spitzlbergerj/CarreraBoxenManager/images/AnsichtHinten.png

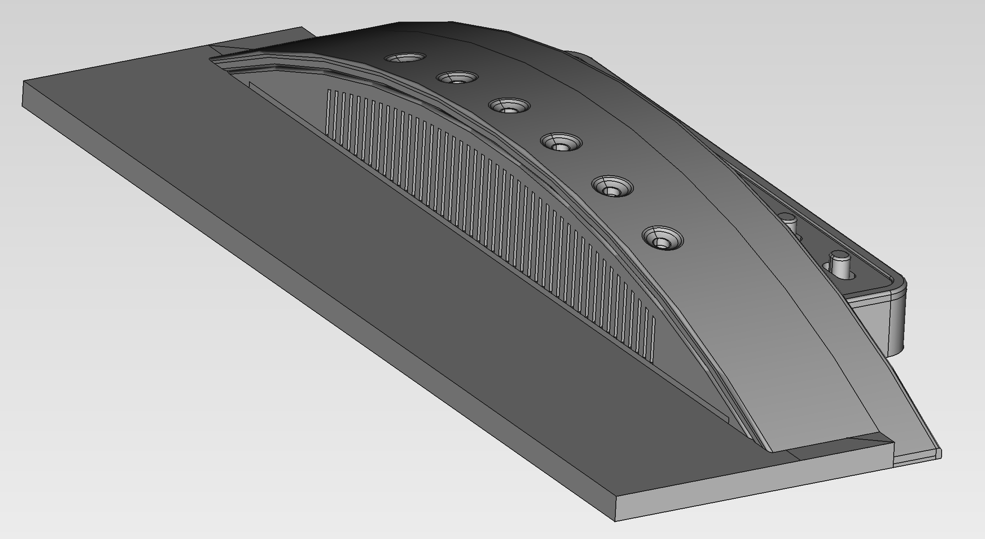
images/AnsichtHinten.png
