spitzlbergerj/CarreraBoxenManager/images/BoxenManager-LED-Platine.jpg

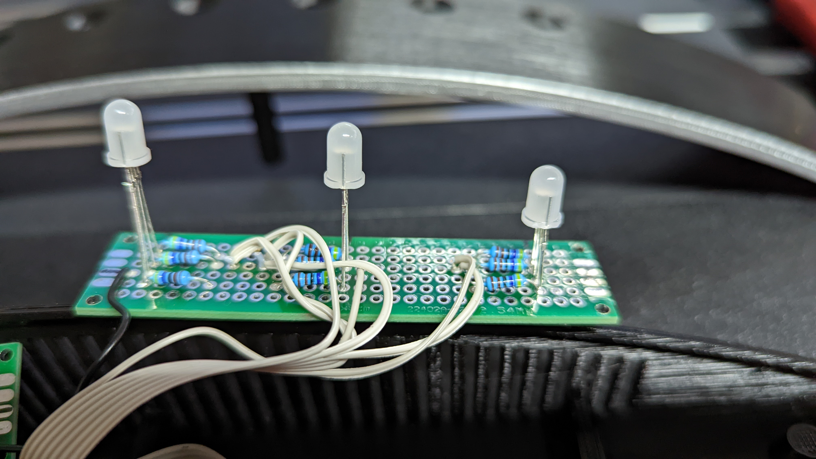
images/BoxenManager-LED-Platine.jpg
