spitzlbergerj/CarreraBoxenManager/images/Boxenmanager-Schiene-Endgehaeuse-Unteransicht.jpg

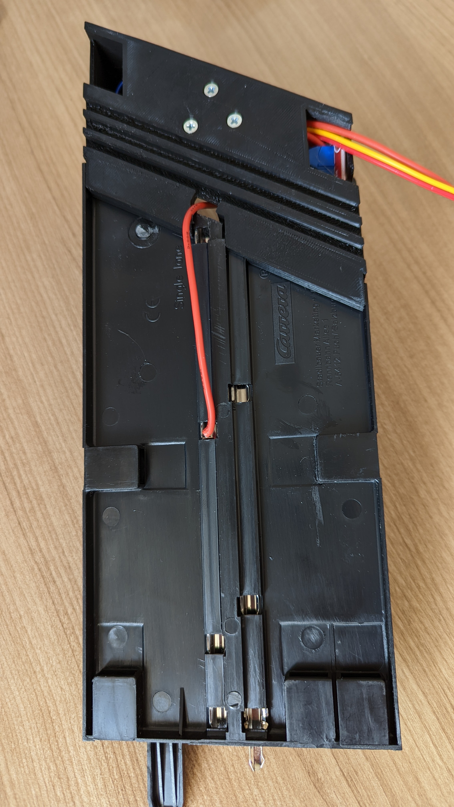
images/Boxenmanager-Schiene-Endgehaeuse-Unteransicht.jpg
