spitzlbergerj/CarreraBoxenManager/images/BoxenManager-Schienenendgehaeuse.jpg

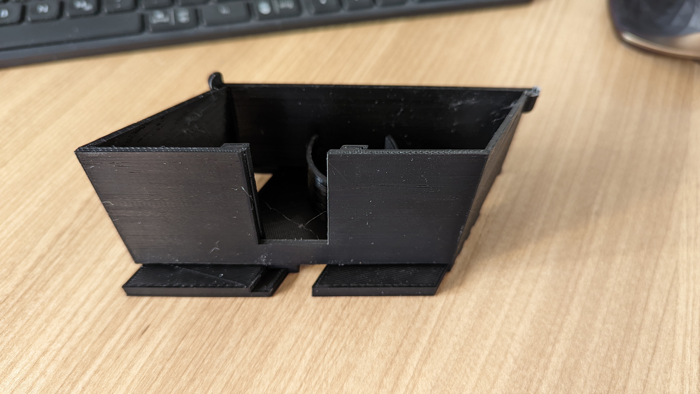
images/BoxenManager-Schienenendgehaeuse.jpg
