spitzlbergerj/CarreraBoxenManager/images/BoxenManager-unter-Bogen-1.jpg

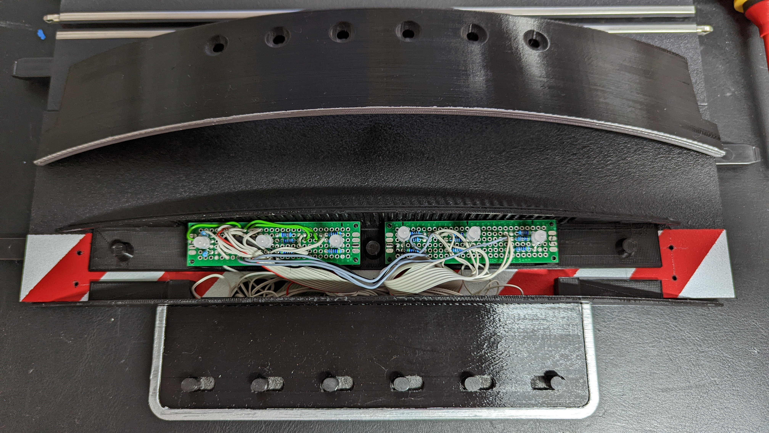
images/BoxenManager-unter-Bogen-1.jpg
