spitzlbergerj/CarreraBoxenManager/images/BoxenManager-Unterseite-1.jpg

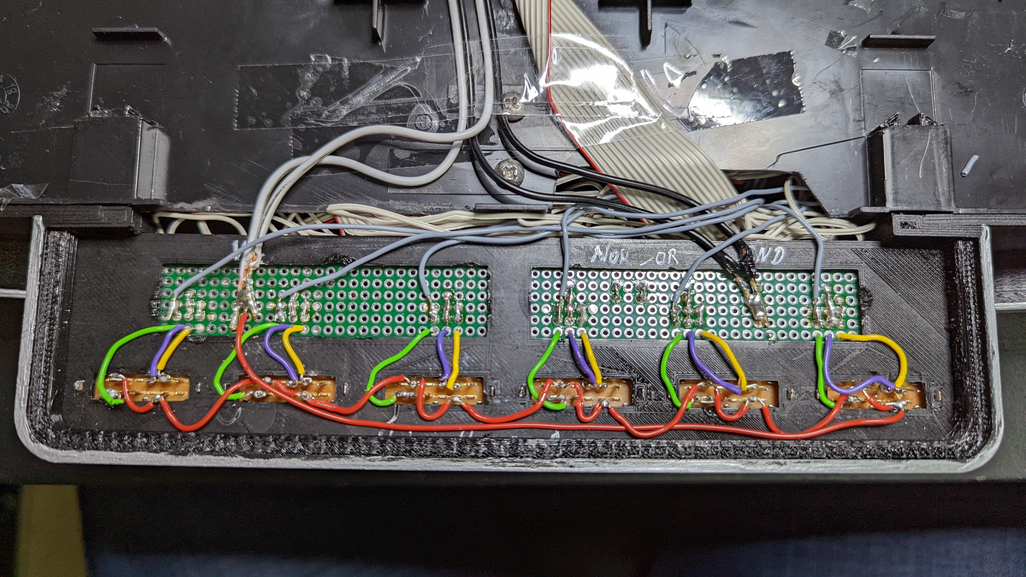
images/BoxenManager-Unterseite-1.jpg
