spitzlbergerj/CarreraBoxenManager/images/BoxenManager-Unterseite-2.jpg

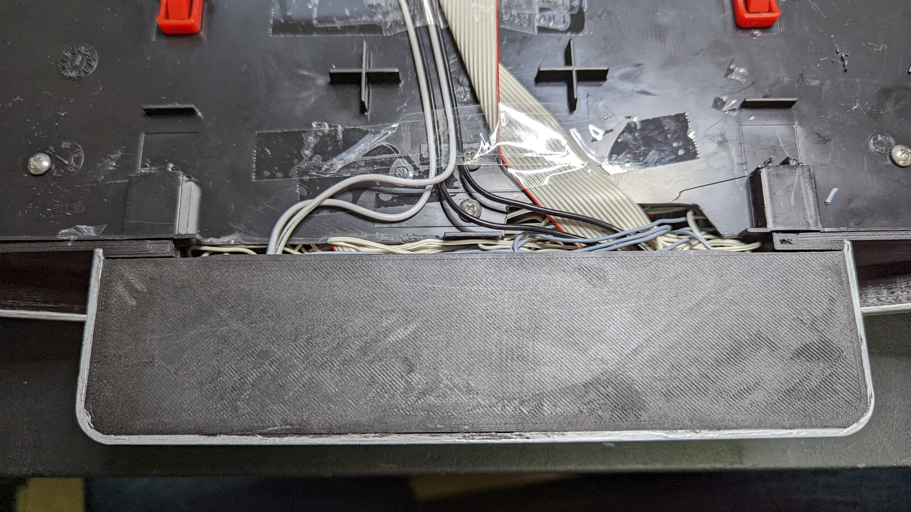
images/BoxenManager-Unterseite-2.jpg
