spitzlbergerj/CarreraBoxenManager/images/BoxenManager-Unterseite-3.jpg

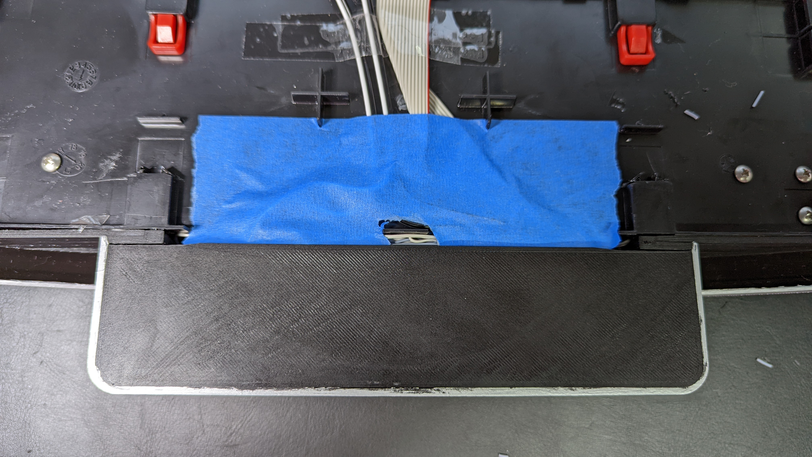
images/BoxenManager-Unterseite-3.jpg
