spitzlbergerj/CarreraBoxenManager/images/BoxenManager-Verbindung-Vorderwand-Bedienteil-zum-Randteil.jpg

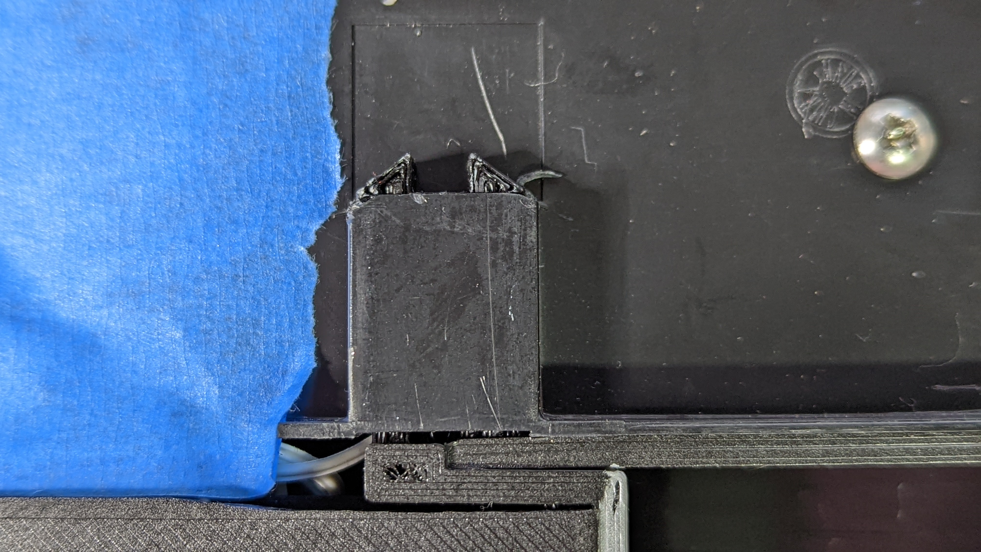
images/BoxenManager-Verbindung-Vorderwand-Bedienteil-zum-Randteil.jpg
