spitzlbergerj/CarreraBoxenManager/images/BoxenManager-Verteiler-BM-uind-ZE.jpg

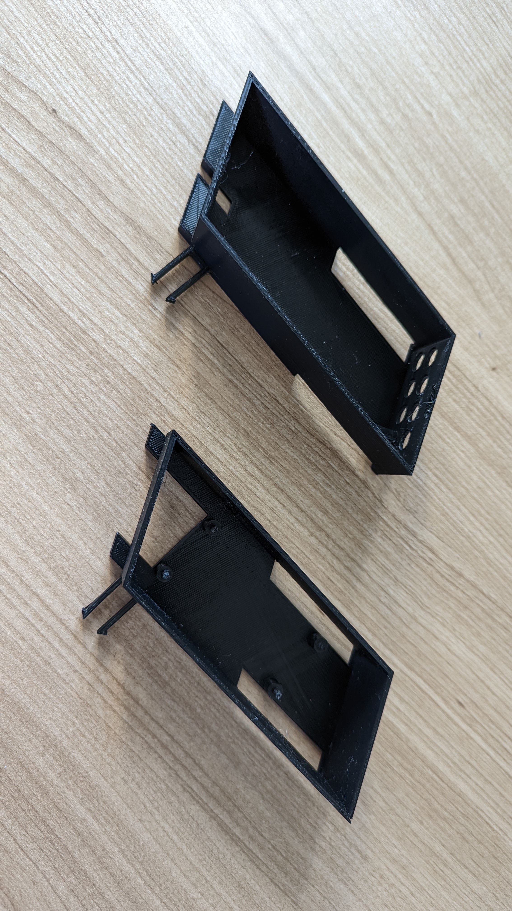
images/BoxenManager-Verteiler-BM-uind-ZE.jpg
