spitzlbergerj/CarreraBoxenManager/images/BoxenManager-Verteiler-BM-ZE.jpg

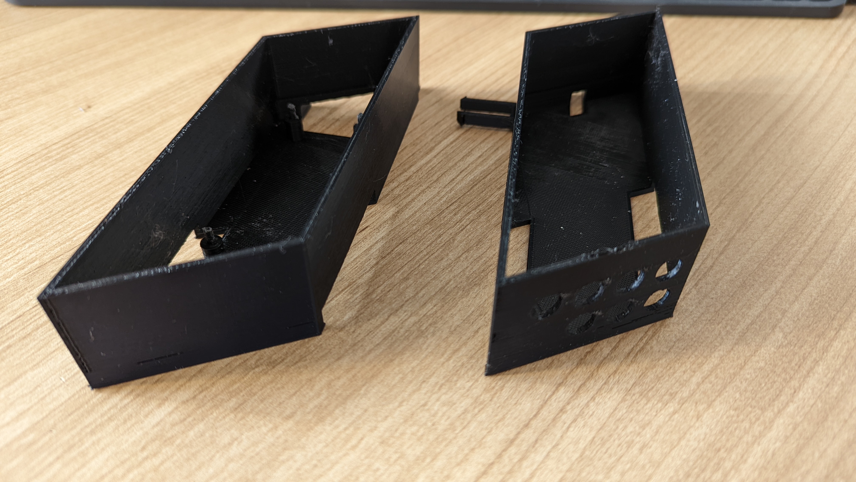
images/BoxenManager-Verteiler-BM-ZE.jpg
